narblaitiin/6sens_prj_stm32wl/hardware/Plots/amplifier/circuit.png

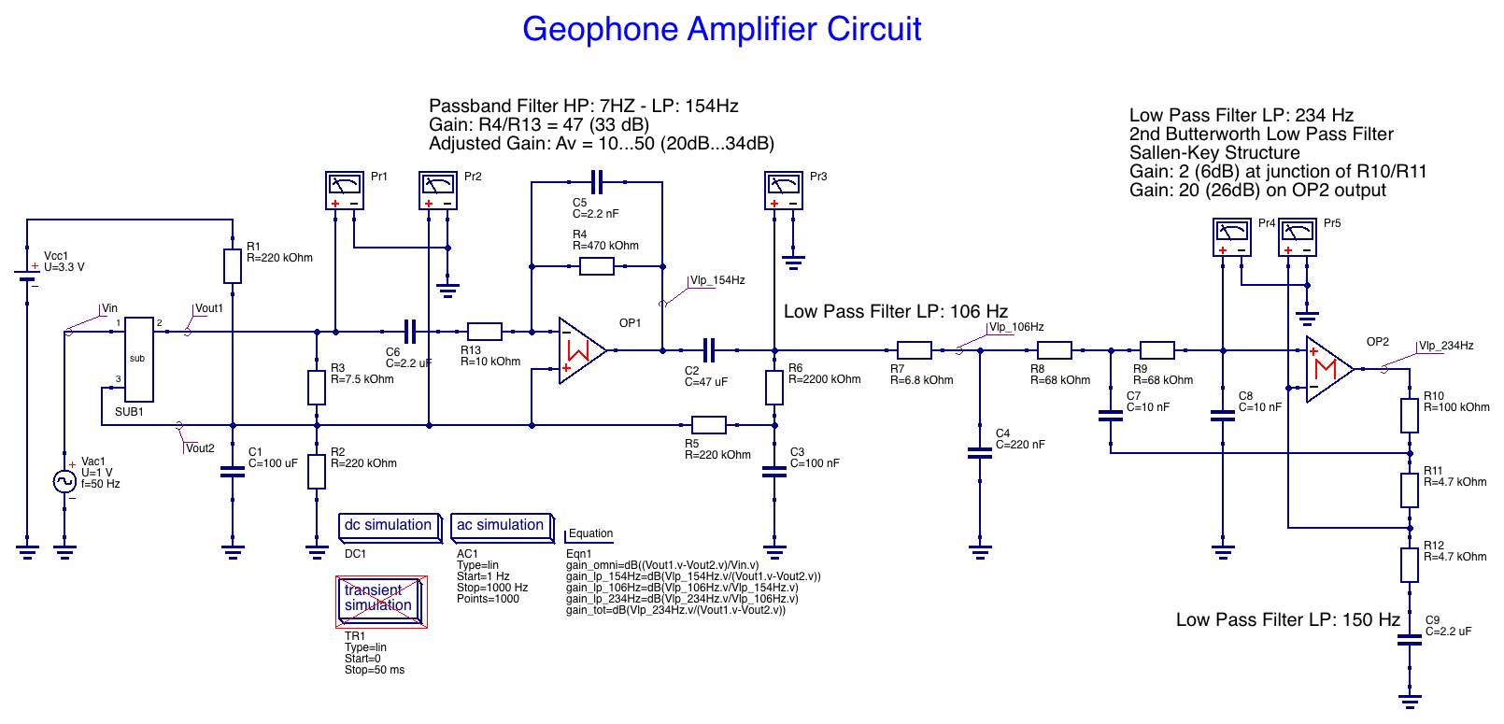
hardware/Plots/amplifier/circuit.png
