narblaitiin/6sens_prj_stm32wl/hardware/Plots/amplifier/filter_3sc_output.png

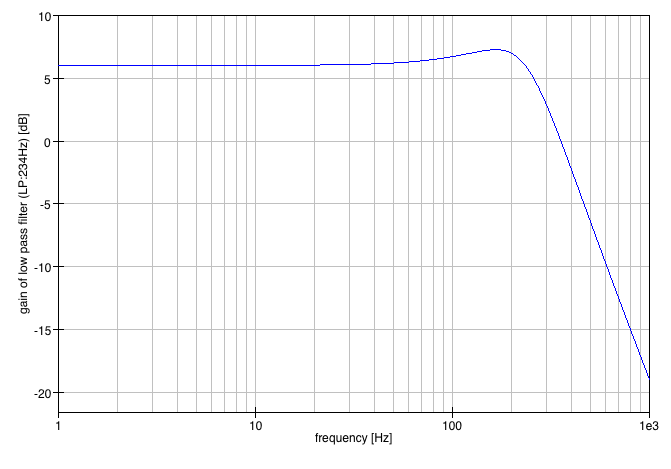
hardware/Plots/amplifier/filter_3sc_output.png
