narblaitiin/6sens_prj_stm32wl/hardware/Plots/geophone/gain_dB.png

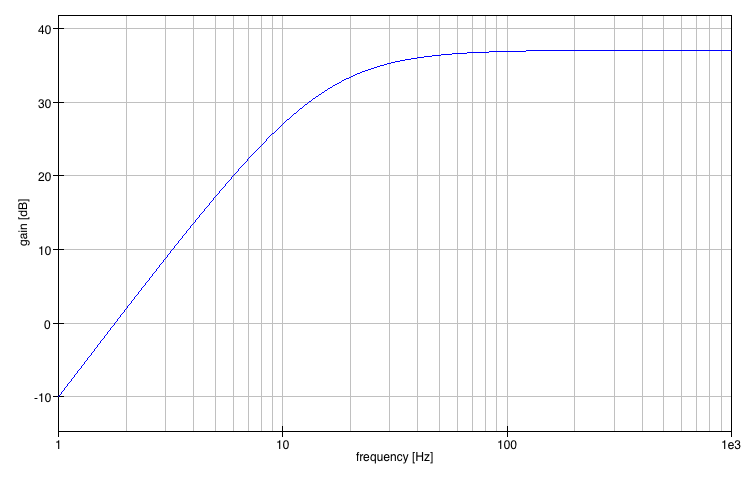
hardware/Plots/geophone/gain_dB.png
