narblaitiin/6sens_prj_stm32wl/hardware/Plots/geophone/sensitivity.png

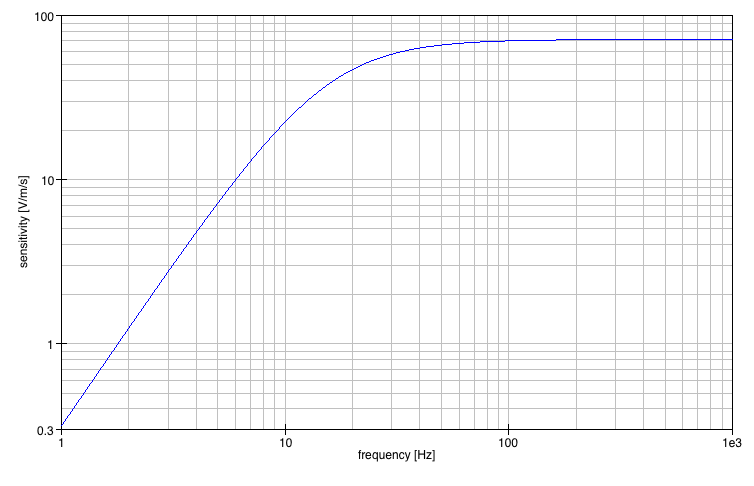
hardware/Plots/geophone/sensitivity.png
