narblaitiin/6sens_prj_stm32wl/firmware/src/app_bme280.h

/*
 * Copyright (c) 2023
 * Regis Rousseau
 * Univ Lyon, INSA Lyon, Inria, CITI, EA3720
 * SPDX-License-Identifier: Apache-2.0
 */

#ifndef APP_BME280_H
#define APP_BME280_H

//  ======== includes ==============================================
#include <zephyr/kernel.h>
#include <zephyr/device.h>
#include <zephyr/drivers/sensor.h>

//  ======== prototypes ============================================
int8_t app_bme280_init(const struct device *dev);
uint16_t app_bme280_get_temp(const struct device *dev);
uint16_t app_bme280_get_press(const struct device *dev);
uint16_t app_bme280_get_hum(const struct device *dev);


#endif /* APP_BME280_H */
